hrvach/deskhop/src/include/pinout.h

/*
 * This file is part of DeskHop (https://github.com/hrvach/deskhop).
 * Copyright (c) 2025 Hrvoje Cavrak
 *
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
 * See the file LICENSE for the full license text.
 */
#pragma once

/*==============================================================================
 *  Board Roles
 *==============================================================================*/

#define BOARD_ROLE (global_state.board_role)
#define OTHER_ROLE (BOARD_ROLE == OUTPUT_A ? OUTPUT_B : OUTPUT_A)

/*==============================================================================
 *  GPIO Pins (LED, USB)
 *==============================================================================*/

#define GPIO_LED_PIN   25 // LED is connected to pin 25 on a PICO
#define PIO_USB_DP_PIN 14 // D+ is pin 14, D- is pin 15

/*==============================================================================
 *  Serial Pins
 *==============================================================================*/

/* GP12 / GP13, Pins 16 (TX), 17 (RX) on the Pico board */
#define BOARD_A_RX 13
#define BOARD_A_TX 12

/* GP16 / GP17, Pins 21 (TX), 22 (RX) on the Pico board */
#define BOARD_B_RX 17
#define BOARD_B_TX 16

#define SERIAL_RX_PIN (global_state.board_role == OUTPUT_A ? BOARD_A_RX : BOARD_B_RX)
#define SERIAL_TX_PIN (global_state.board_role == OUTPUT_A ? BOARD_A_TX : BOARD_B_TX)
