hrvach/deskhop/src/led.c

/*
 * This file is part of DeskHop (https://github.com/hrvach/deskhop).
 * Copyright (c) 2025 Hrvoje Cavrak
 *
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
 * See the file LICENSE for the full license text.
 */

#include "main.h"

/* ==================================================== *
 * ========== Update pico and keyboard LEDs  ========== *
 * ==================================================== */

void set_keyboard_leds(uint8_t requested_led_state, device_t *state) {
    static uint8_t new_led_value;

    new_led_value = requested_led_state;
    if (state->keyboard_connected) {
        if(tuh_hid_set_report(state->kbd_dev_addr,
                              state->kbd_instance,
                              0,
                              HID_REPORT_TYPE_OUTPUT,
                              &new_led_value,
                              sizeof(uint8_t)))

            state->keyboard_leds_actual[BOARD_ROLE] = requested_led_state;
    }
}

void restore_leds(device_t *state) {
    /* Light up on-board LED if current board is active output */
    state->onboard_led_state = (state->active_output == BOARD_ROLE);
    gpio_put(GPIO_LED_PIN, state->onboard_led_state);

    /* Light up appropriate keyboard leds (if it's connected locally) */
    if (state->keyboard_connected) {
        uint8_t leds = state->keyboard_leds_desired[state->active_output];
        set_keyboard_leds(leds, state);
    }
}

uint8_t toggle_led(void) {
    uint8_t new_led_state = gpio_get(GPIO_LED_PIN) ^ 1;
    gpio_put(GPIO_LED_PIN, new_led_state);

    return new_led_state;
}

void blink_led(device_t *state) {
    /* Since LEDs might be ON previously, we go OFF, ON, OFF, ON, OFF */
    state->blinks_left     = 5;
    state->last_led_change = time_us_32();
}

void led_sync_task(device_t *state) {
    /* Check if keyboard LEDs need to be updated */
    if (state->keyboard_connected) {
        uint8_t desired_leds = state->keyboard_leds_desired[state->active_output];

        if (state->keyboard_leds_actual[BOARD_ROLE] != desired_leds)
            set_keyboard_leds(desired_leds, state);
    }
}

void led_blinking_task(device_t *state) {
    const int blink_interval_us = 80000; /* 80 ms off, 80 ms on */
    static uint8_t leds;

    /* If there is no more blinking to be done, exit immediately */
    if (state->blinks_left == 0)
        return;

    /* We have some blinks left to do, check if they are due, exit if not */
    if ((time_us_32()) - state->last_led_change < blink_interval_us)
        return;

    /* Toggle the LED state */
    uint8_t new_led_state = toggle_led();

    /* Also keyboard leds (if it's connected locally) since on-board leds are not visible */
    leds = new_led_state * 0x07; /* Numlock, capslock, scrollock */

    if (state->keyboard_connected)
        set_keyboard_leds(leds, state);

    /* Decrement the counter and update the last-changed timestamp */
    state->blinks_left--;
    state->last_led_change = time_us_32();

    /* Restore LEDs in the last pass */
    if (state->blinks_left == 0)
        restore_leds(state);
}
