hrvach/deskhop/src/defaults.c

/*
 * This file is part of DeskHop (https://github.com/hrvach/deskhop).
 * Copyright (c) 2025 Hrvoje Cavrak
 *
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
 * See the file LICENSE for the full license text.
 */
#include "main.h"

/* Default configuration */
const config_t default_config = {
    .magic_header = 0xB00B1E5,
    .version = CURRENT_CONFIG_VERSION,
    .output[OUTPUT_A] =
        {
            .number = OUTPUT_A,
            .speed_x = MOUSE_SPEED_A_FACTOR_X,
            .speed_y = MOUSE_SPEED_A_FACTOR_Y,
            .border = {
                .top = 0,
                .bottom = MAX_SCREEN_COORD,
            },
            .screen_count = 1,
            .screen_index = 1,
            .os = OUTPUT_A_OS,
            .pos = RIGHT,
            .screensaver = {
                .mode = SCREENSAVER_A_MODE,
                .only_if_inactive = SCREENSAVER_A_ONLY_IF_INACTIVE,
                .idle_time_us = (uint64_t)SCREENSAVER_A_IDLE_TIME_SEC * 1000000,
                .max_time_us = (uint64_t)SCREENSAVER_A_MAX_TIME_SEC * 1000000,
            }
        },
    .output[OUTPUT_B] =
        {
            .number = OUTPUT_B,
            .speed_x = MOUSE_SPEED_B_FACTOR_X,
            .speed_y = MOUSE_SPEED_B_FACTOR_Y,
            .border = {
                .top = 0,
                .bottom = MAX_SCREEN_COORD,
            },
            .screen_count = 1,
            .screen_index = 1,
            .os = OUTPUT_B_OS,
            .pos = LEFT,
            .screensaver = {
                .mode = SCREENSAVER_B_MODE,
                .only_if_inactive = SCREENSAVER_B_ONLY_IF_INACTIVE,
                .idle_time_us = (uint64_t)SCREENSAVER_B_IDLE_TIME_SEC * 1000000,
                .max_time_us = (uint64_t)SCREENSAVER_B_MAX_TIME_SEC * 1000000,
            }
        },
    .enforce_ports = ENFORCE_PORTS,
    .force_kbd_boot_protocol = ENFORCE_KEYBOARD_BOOT_PROTOCOL,
    .force_mouse_boot_mode = false,
    .enable_acceleration = ENABLE_ACCELERATION,
    .hotkey_toggle = HOTKEY_TOGGLE,
    .kbd_led_as_indicator = KBD_LED_AS_INDICATOR,
    .jump_threshold = JUMP_THRESHOLD,
};
