hrvach/deskhop/Pico-PIO-USB/src/pio_usb.h

#pragma once

#include "pio_usb_configuration.h"
#include "usb_definitions.h"

#ifdef __cplusplus
 extern "C" {
#endif

// Host functions
usb_device_t *pio_usb_host_init(const pio_usb_configuration_t *c);
int pio_usb_host_add_port(uint8_t pin_dp, PIO_USB_PINOUT pinout);
void pio_usb_host_task(void);
void pio_usb_host_stop(void);
void pio_usb_host_restart(void);
uint32_t pio_usb_host_get_frame_number(void);

// Call this every 1ms when skip_alarm_pool is true.
void pio_usb_host_frame(void);

// Device functions
usb_device_t *pio_usb_device_init(const pio_usb_configuration_t *c,
                                  const usb_descriptor_buffers_t *buffers);
void pio_usb_device_task(void);

// Common functions
endpoint_t *pio_usb_get_endpoint(usb_device_t *device, uint8_t idx);
int pio_usb_get_in_data(endpoint_t *ep, uint8_t *buffer, uint8_t len);
int pio_usb_set_out_data(endpoint_t *ep, const uint8_t *buffer, uint8_t len);

// Misc functions
int pio_usb_kbd_set_leds(usb_device_t *device, uint8_t port, uint8_t value); 

extern int dh_debug_printf(const char *format, ...);

#ifdef __cplusplus
 }
#endif
